ataruno/Mooose/forCaseDesign/forCaseDesign_image/ケース設計用09.png

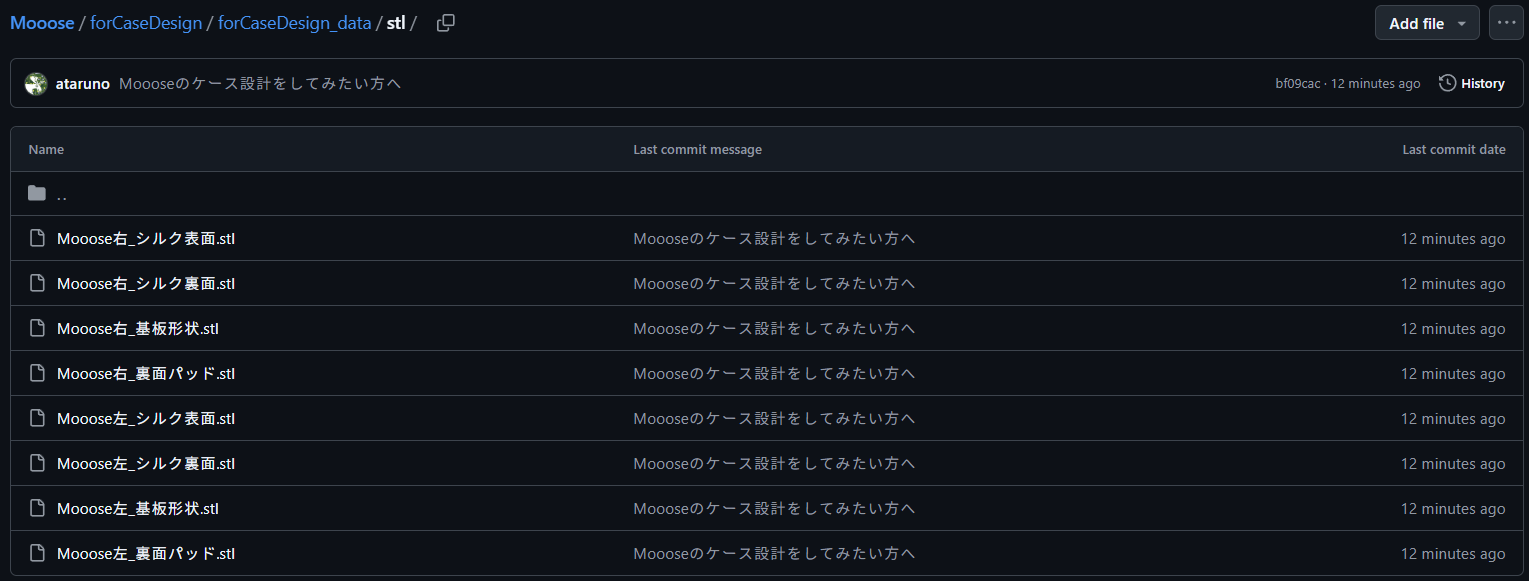
forCaseDesign/forCaseDesign_image/ケース設計用09.png
