ataruno/Mooose/build_guide/build_guide_image_hard/Mooose_背面.jpg

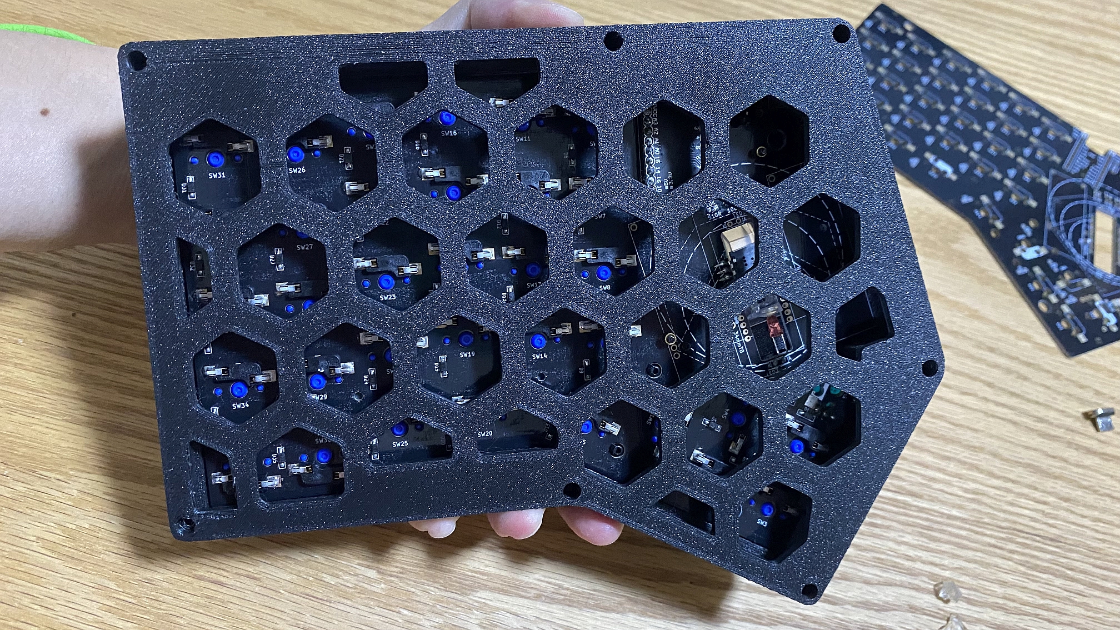
build_guide/build_guide_image_hard/Mooose_背面.jpg
