ataruno/Mooose/build_guide/build_guide_image_remap/51_remapへアクセス.jpg

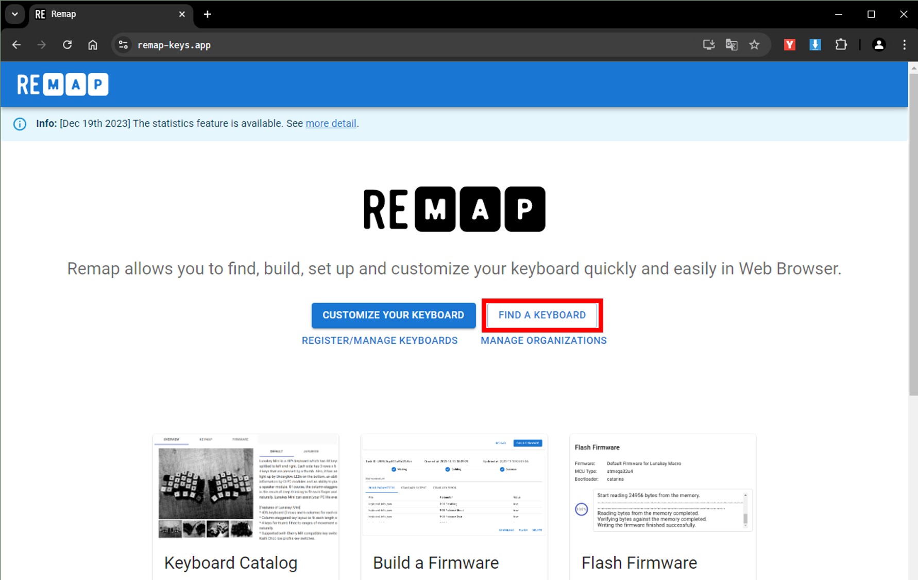
build_guide/build_guide_image_remap/51_remapへアクセス.jpg
